MarcoFranchi/smart-fridge-magnet/IMG_0268 (2).jpg

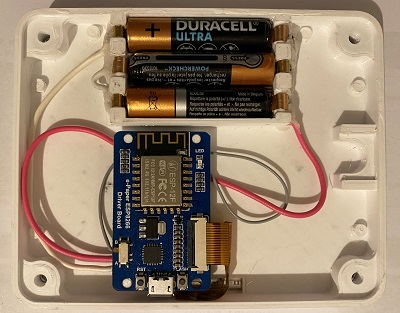
IMG_0268 (2).jpg
