MarcoFranchi/smart-fridge-magnet/IMG_0283 (2).jpg

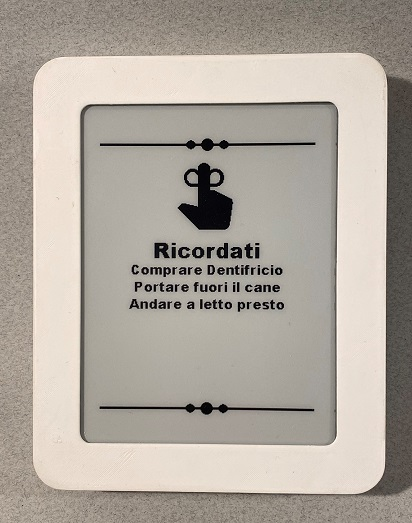
IMG_0283 (2).jpg
